yonush/PicoPLC/Photos/rev1/Pico PLC (no Pico) 1.jpg

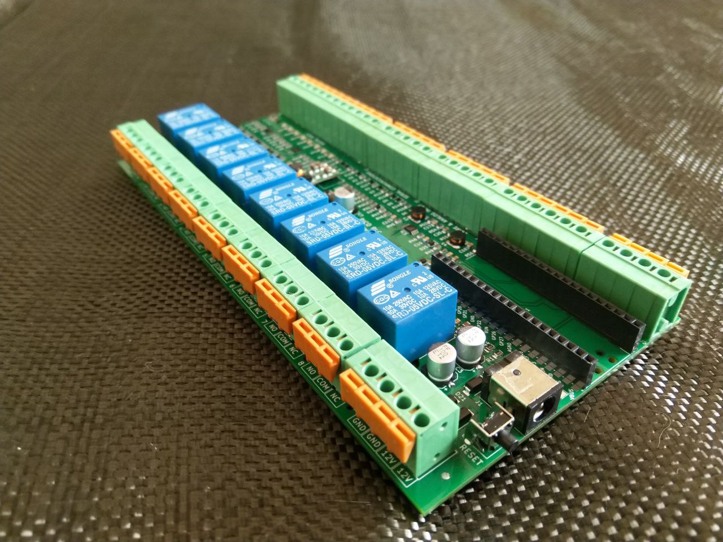
Photos/rev1/Pico PLC (no Pico) 1.jpg
