yonush/PicoPLC/Photos/rev1/Pico PLC (no Pico) 2.jpg

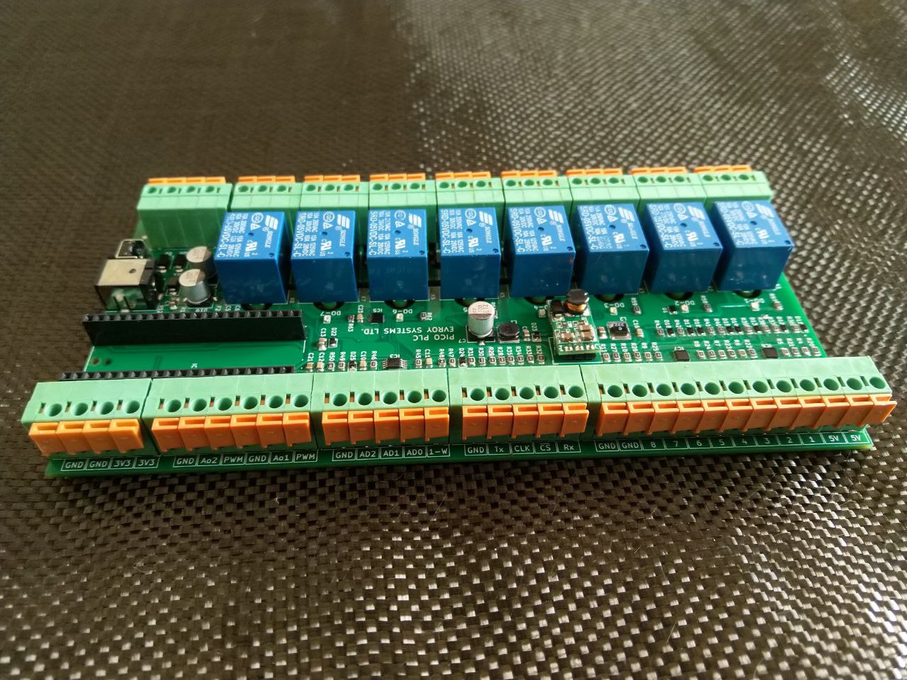
Photos/rev1/Pico PLC (no Pico) 2.jpg
