yonush/PicoPLC/Photos/rev1/Pico PLC (no Pico) 3.jpg

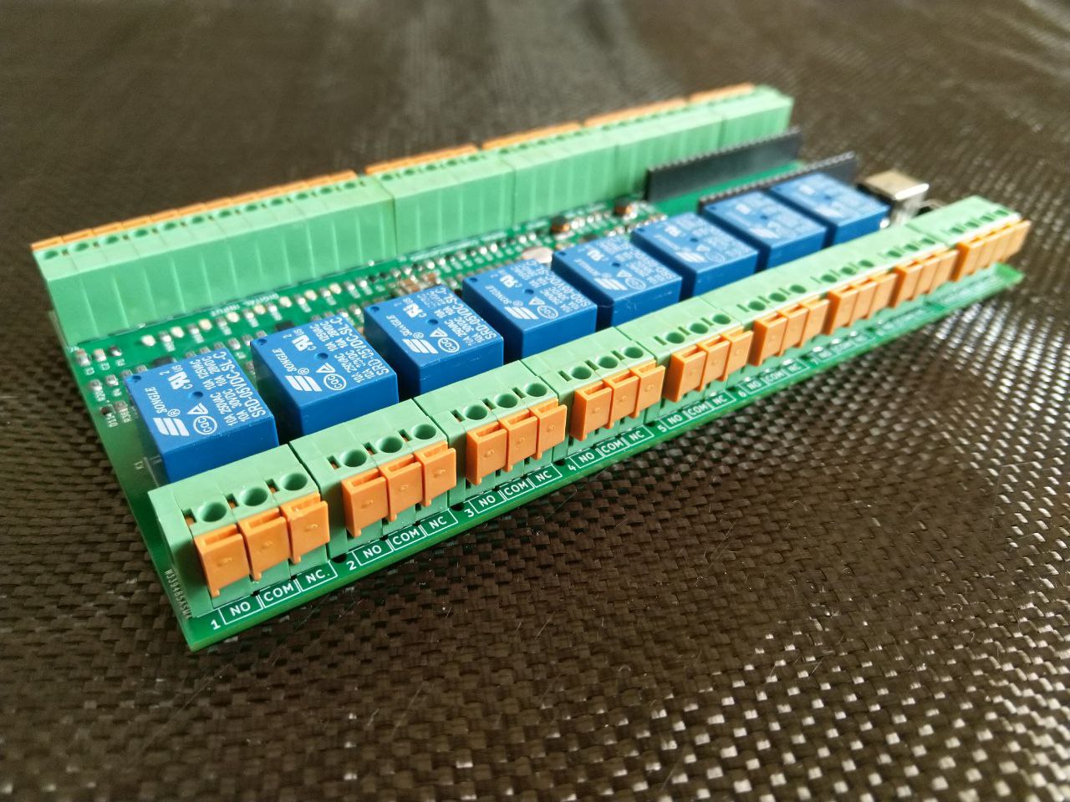
Photos/rev1/Pico PLC (no Pico) 3.jpg
