yonush/PicoPLC/Photos/rev1/Pico PLC (no Pico) 4.jpg

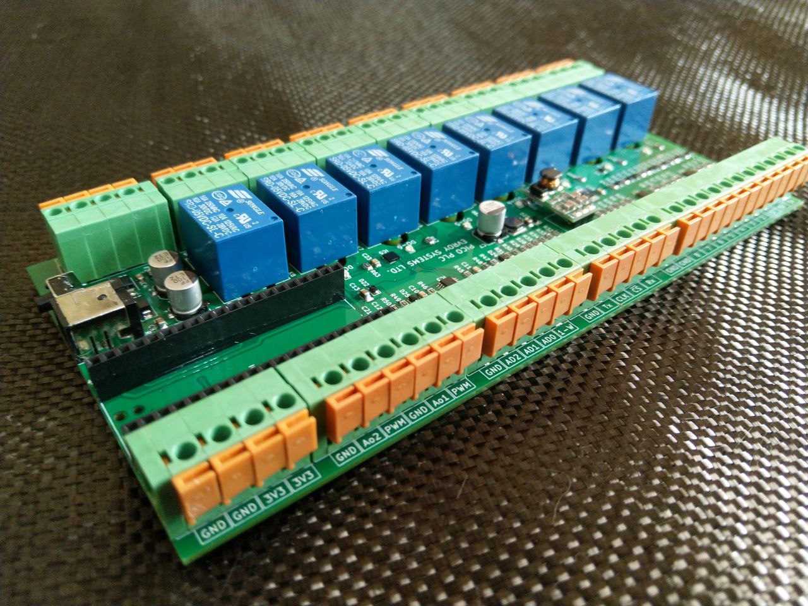
Photos/rev1/Pico PLC (no Pico) 4.jpg
