yonush/PicoPLC/Photos/rev1/Pico PLC (no Pico) 5.jpg

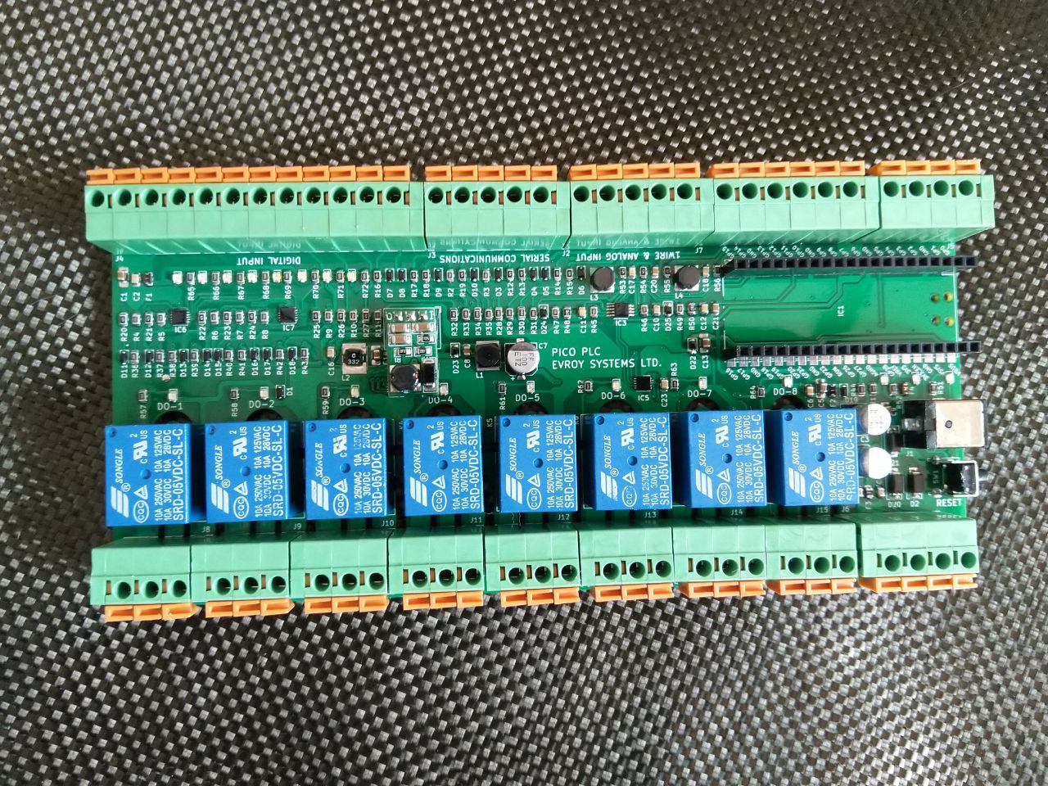
Photos/rev1/Pico PLC (no Pico) 5.jpg
