yonush/PicoPLC/Photos/rev1/Pico PLC (no Pico) 6.jpg

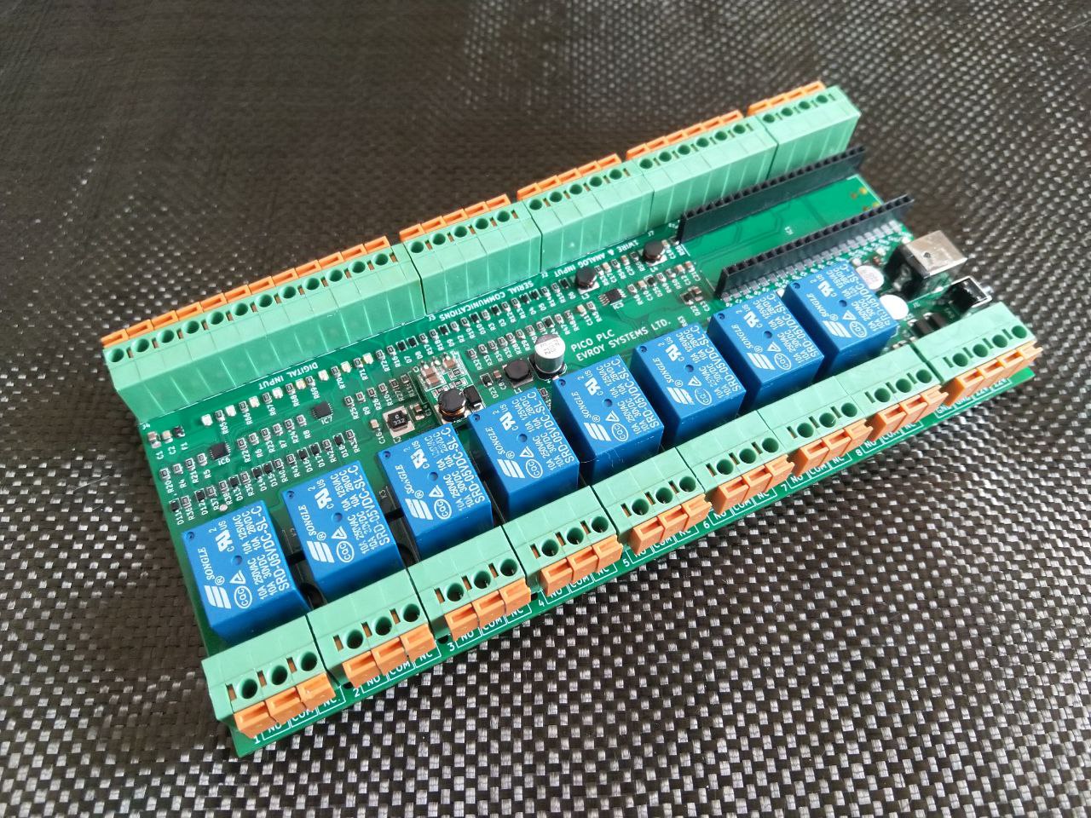
Photos/rev1/Pico PLC (no Pico) 6.jpg
