yonush/PicoPLC/Photos/rev1/Pico PLC using leaded Pico 1.jpg

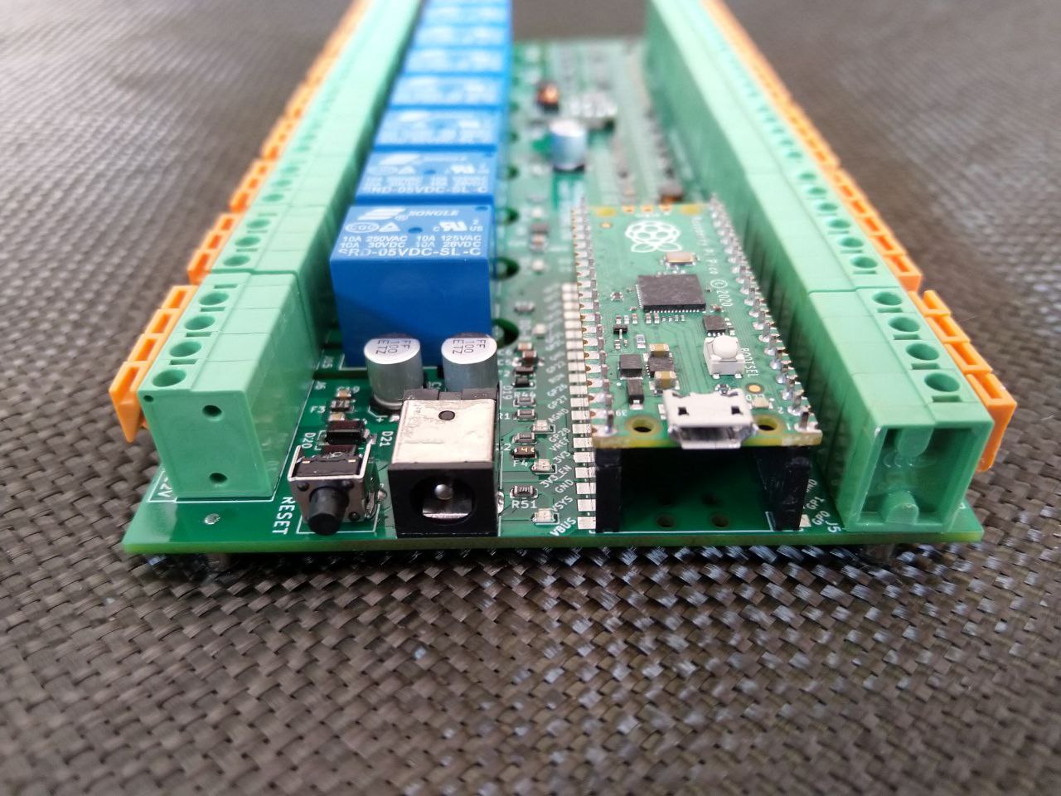
Photos/rev1/Pico PLC using leaded Pico 1.jpg
