yonush/PicoPLC/Photos/rev1/Pico PLC using leaded Pico 2.jpg

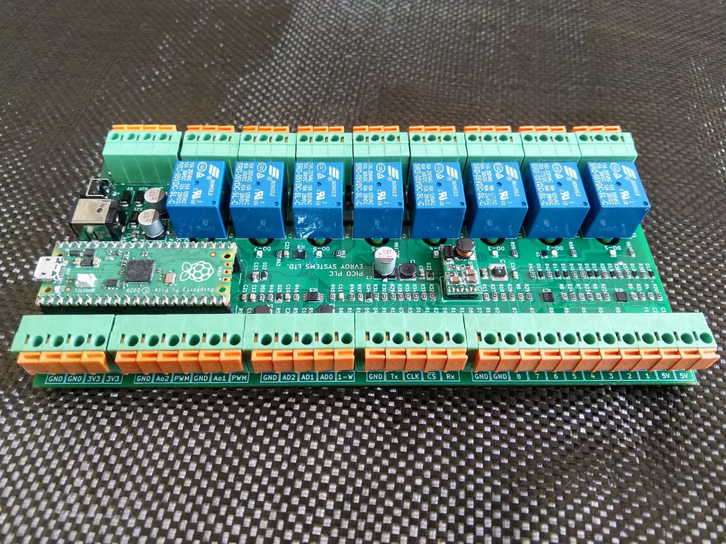
Photos/rev1/Pico PLC using leaded Pico 2.jpg
