yonush/PicoPLC/Photos/rev1/Pico PLC using leaded Pico 4.jpg

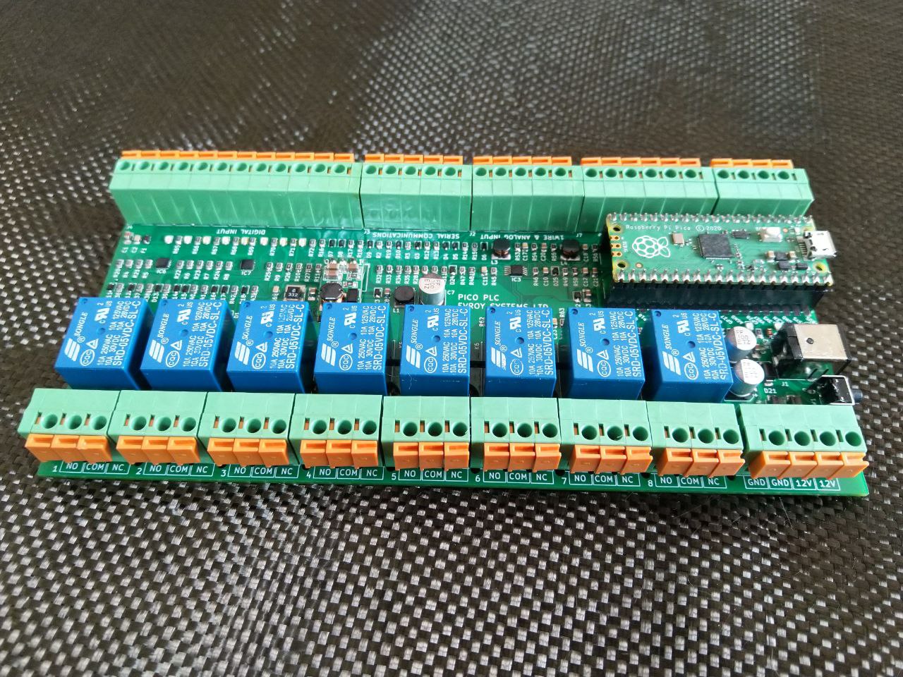
Photos/rev1/Pico PLC using leaded Pico 4.jpg
