yonush/PicoPLC/Photos/rev1/Pico PLC using leaded Pico 5.jpg

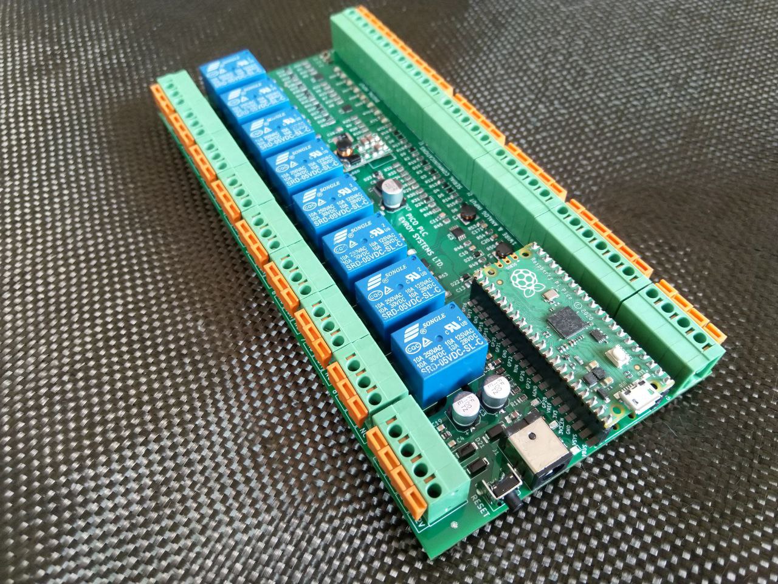
Photos/rev1/Pico PLC using leaded Pico 5.jpg
