yonush/PicoPLC/Photos/rev1/PicoPLC using Pico-W1.jpg

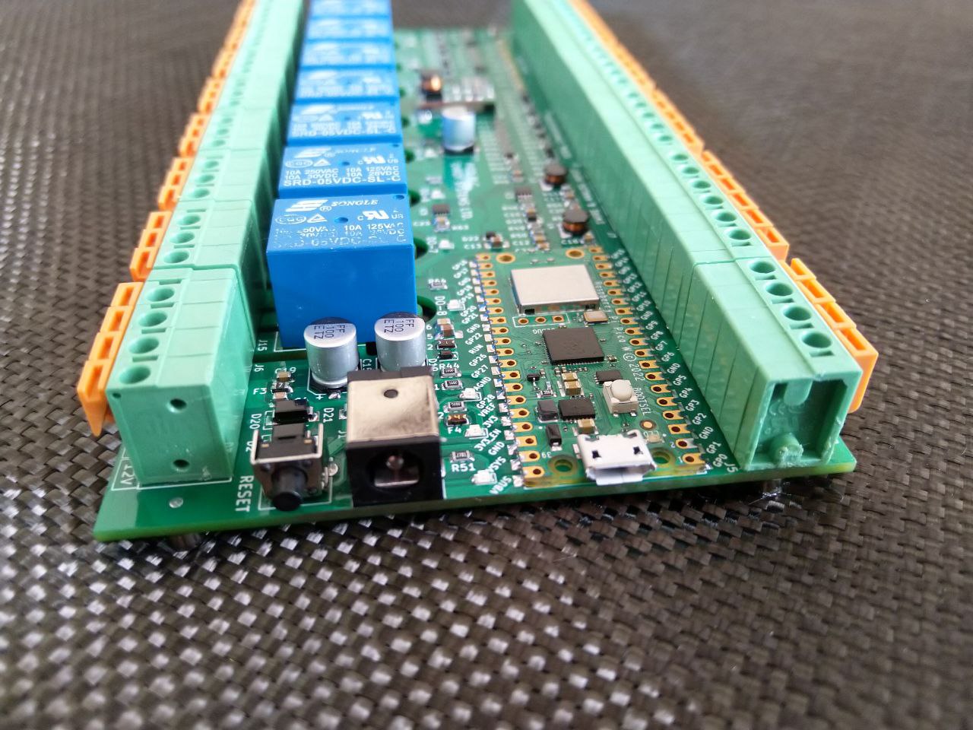
Photos/rev1/PicoPLC using Pico-W1.jpg
