yonush/PicoPLC/Photos/rev1/PicoPLC using Pico-W2.jpg

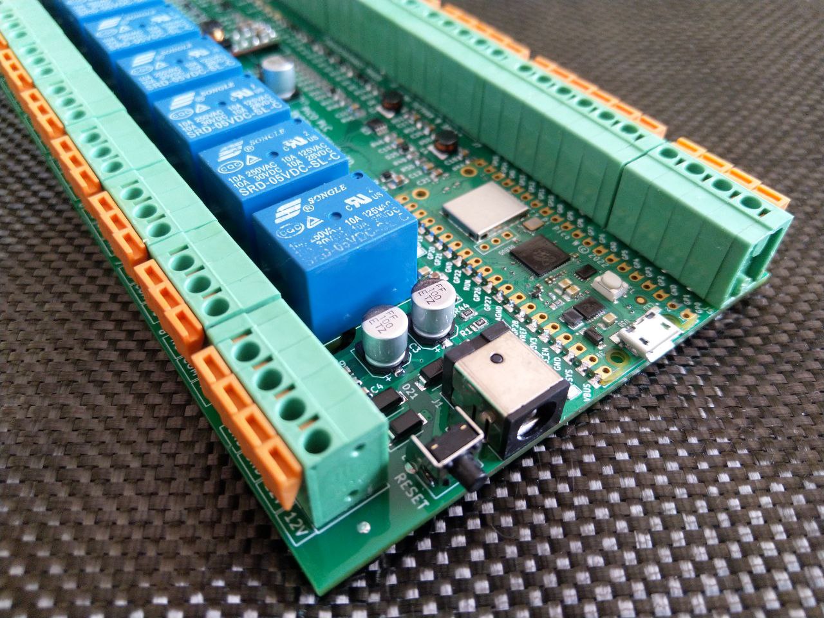
Photos/rev1/PicoPLC using Pico-W2.jpg
