yonush/PicoPLC/Photos/rev1/PicoPLC using Pico-W3.jpg

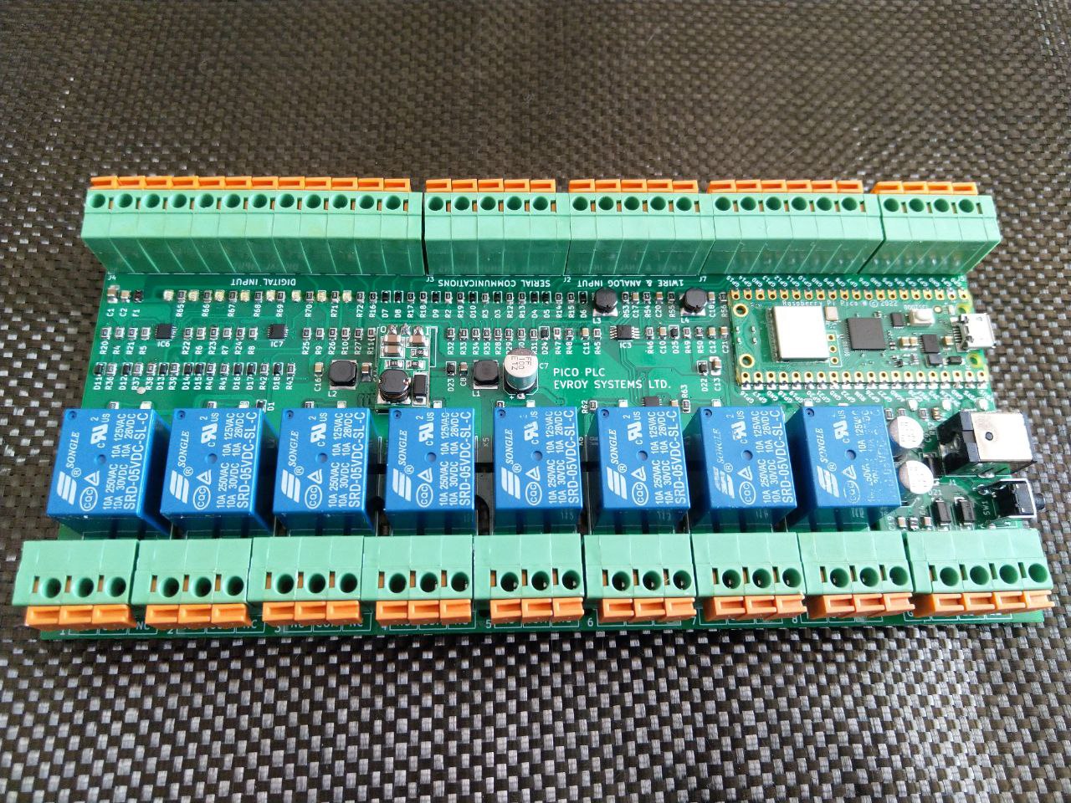
Photos/rev1/PicoPLC using Pico-W3.jpg
