yonush/PicoPLC/Documents/DAC & PWM tests/5V DC blip 1.jpeg

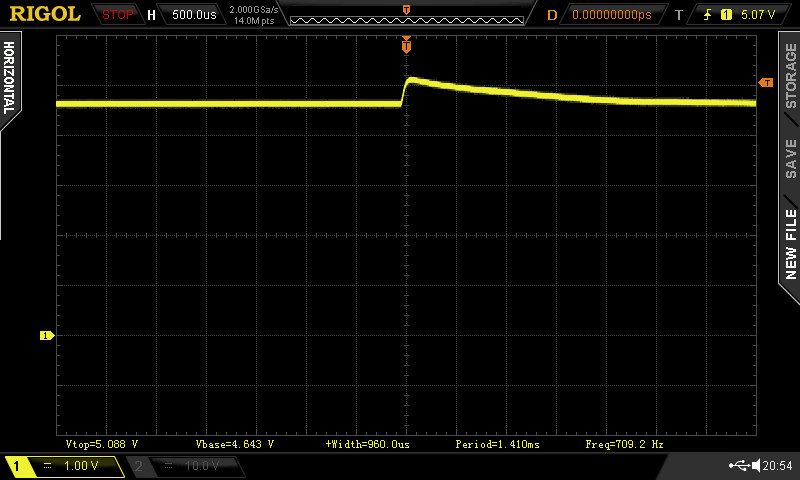
Documents/DAC & PWM tests/5V DC blip 1.jpeg
