yonush/PicoPLC/Documents/DAC & PWM tests/5V rail on 12V turn on (no USB power).jpeg

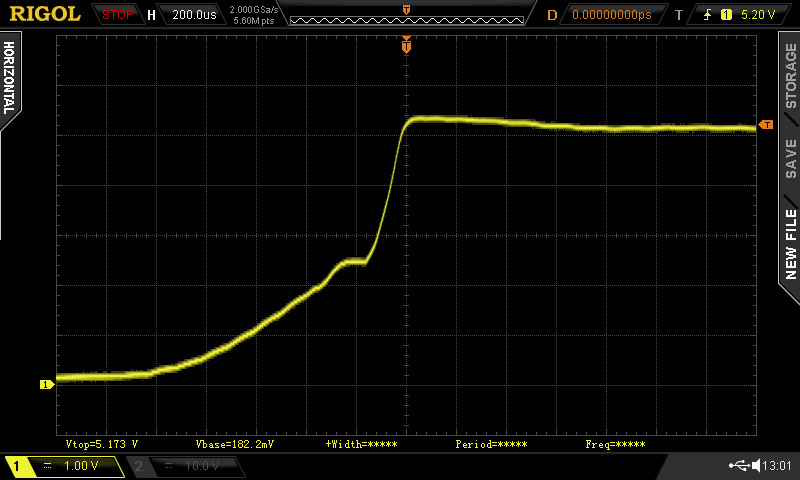
Documents/DAC & PWM tests/5V rail on 12V turn on (no USB power).jpeg
