yonush/PicoPLC/Documents/DAC & PWM tests/DAC & PWM Output/10kHz/10 Percent Dutycycle.png

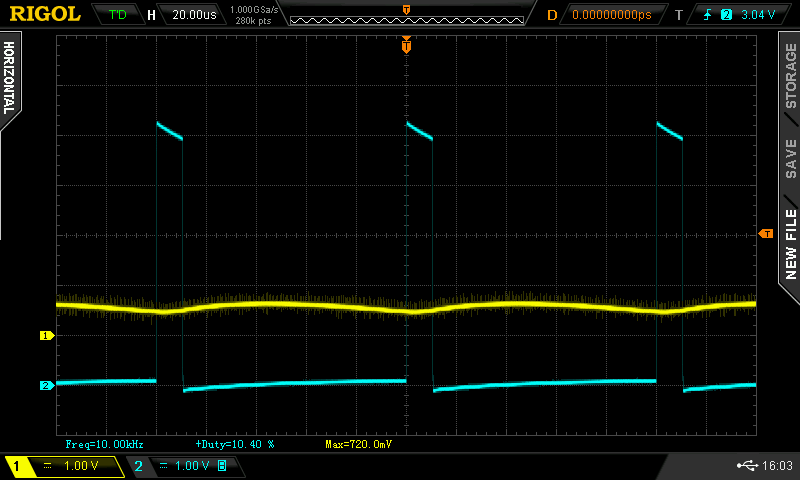
Documents/DAC & PWM tests/DAC & PWM Output/10kHz/10 Percent Dutycycle.png
