yonush/PicoPLC/Documents/DAC & PWM tests/DAC & PWM Output/10kHz/37 Percent Dutycycle.png

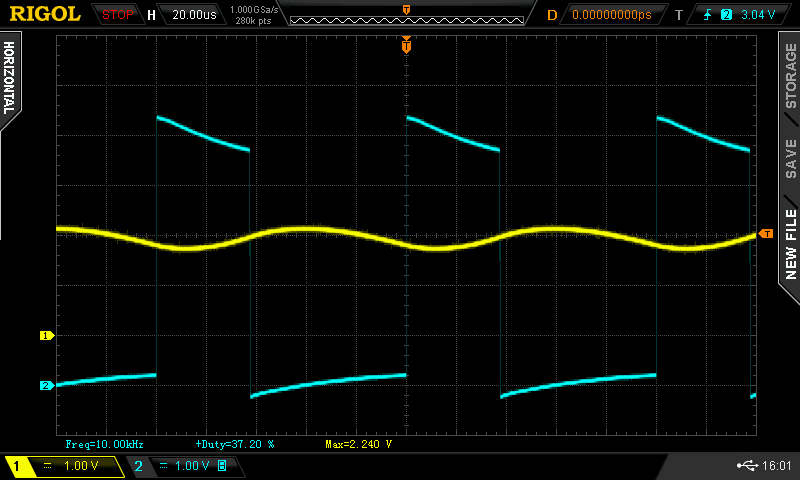
Documents/DAC & PWM tests/DAC & PWM Output/10kHz/37 Percent Dutycycle.png
