yonush/PicoPLC/Documents/DAC & PWM tests/DAC & PWM Output/25kHz/10 Percent Dutycycle.png

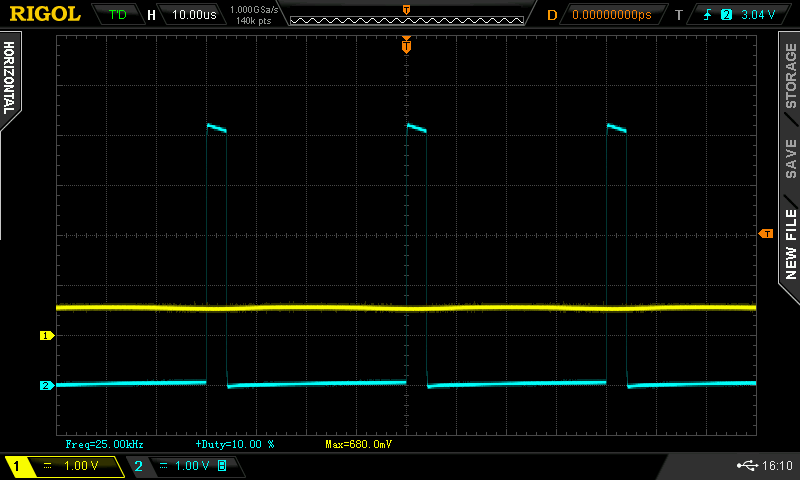
Documents/DAC & PWM tests/DAC & PWM Output/25kHz/10 Percent Dutycycle.png
