yonush/PicoPLC/Documents/DAC & PWM tests/DAC & PWM Output/25kHz/50 Percent Dutycycle.png

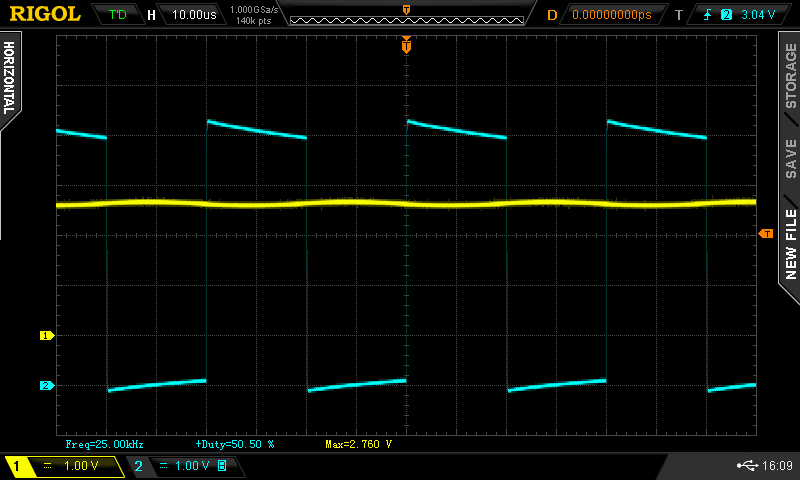
Documents/DAC & PWM tests/DAC & PWM Output/25kHz/50 Percent Dutycycle.png
