yonush/PicoPLC/Documents/DAC & PWM tests/DAC & PWM Output/25kHz/75 Percent Dutycycle.png

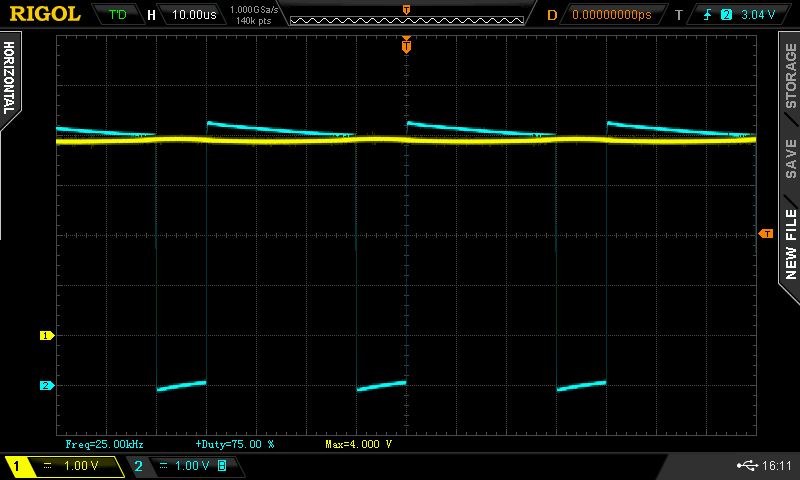
Documents/DAC & PWM tests/DAC & PWM Output/25kHz/75 Percent Dutycycle.png
