yonush/PicoPLC/Documents/DAC & PWM tests/DAC & PWM Output/25kHz/83 Percent Dutycycle.png

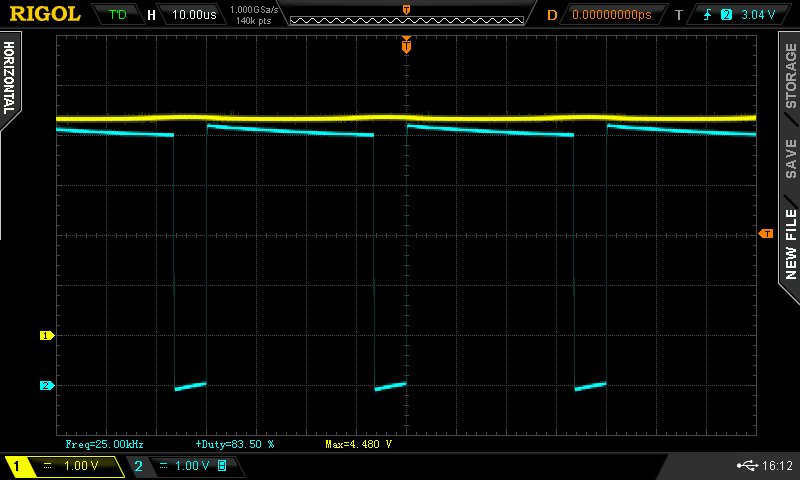
Documents/DAC & PWM tests/DAC & PWM Output/25kHz/83 Percent Dutycycle.png
