yonush/PicoPLC/Documents/DAC & PWM tests/Falling edge 2.jpeg

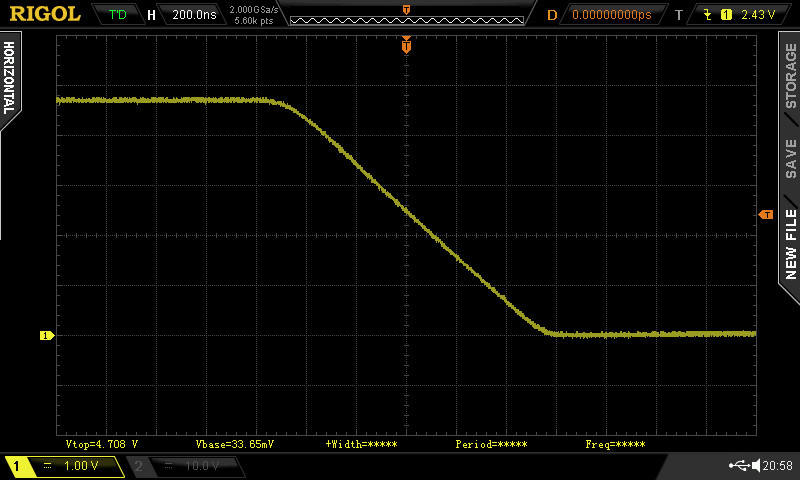
Documents/DAC & PWM tests/Falling edge 2.jpeg
