yonush/PicoPLC/Documents/DAC & PWM tests/Rising edge 1.jpeg

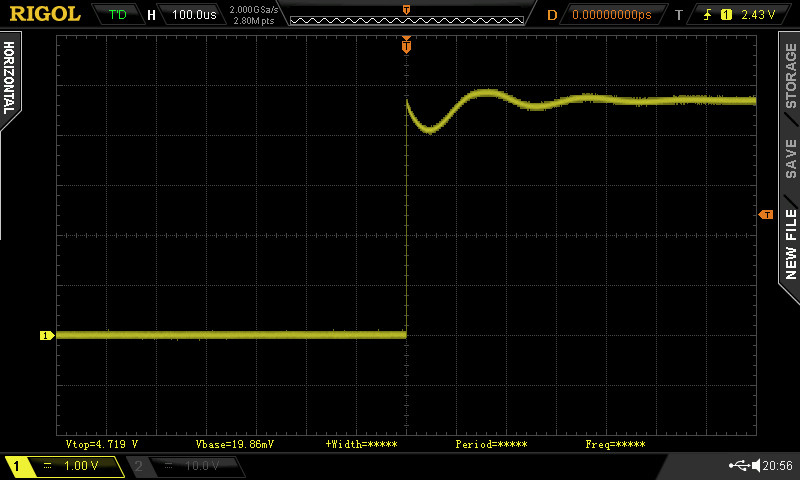
Documents/DAC & PWM tests/Rising edge 1.jpeg
